RCarapinha/PreampPAL/Simulation/2.JPG

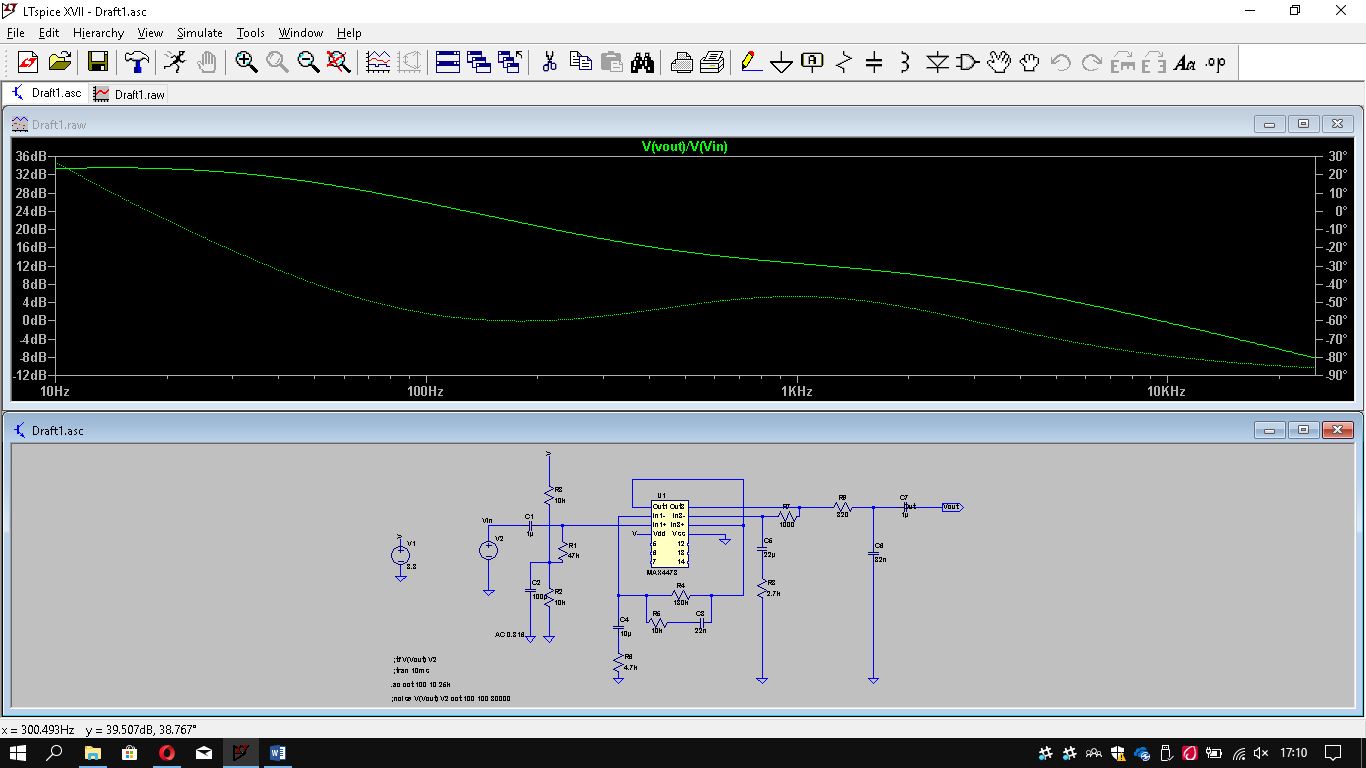
Simulation/2.JPG
