RCarapinha/PreampPAL/Simulation/3.JPG

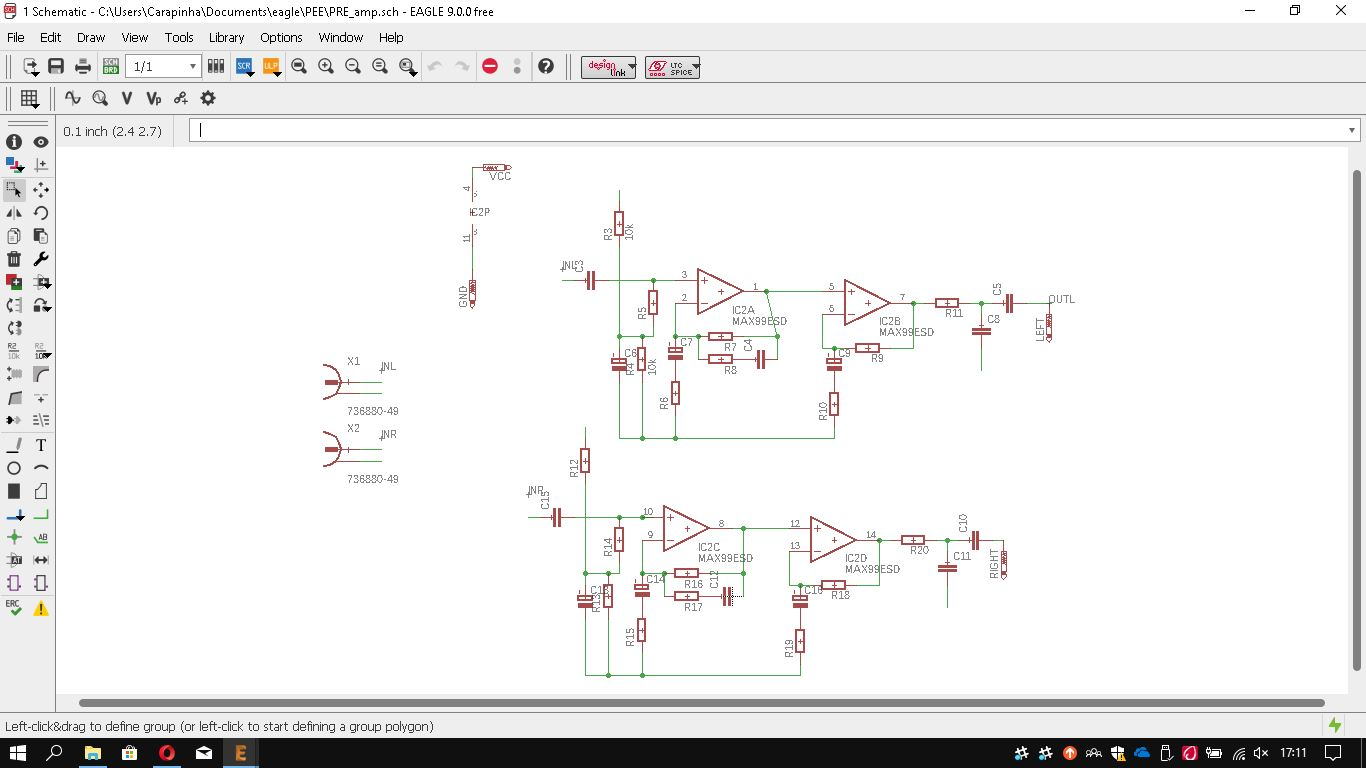
Simulation/3.JPG
