RCarapinha/PreampPAL/Simulation/4.JPG

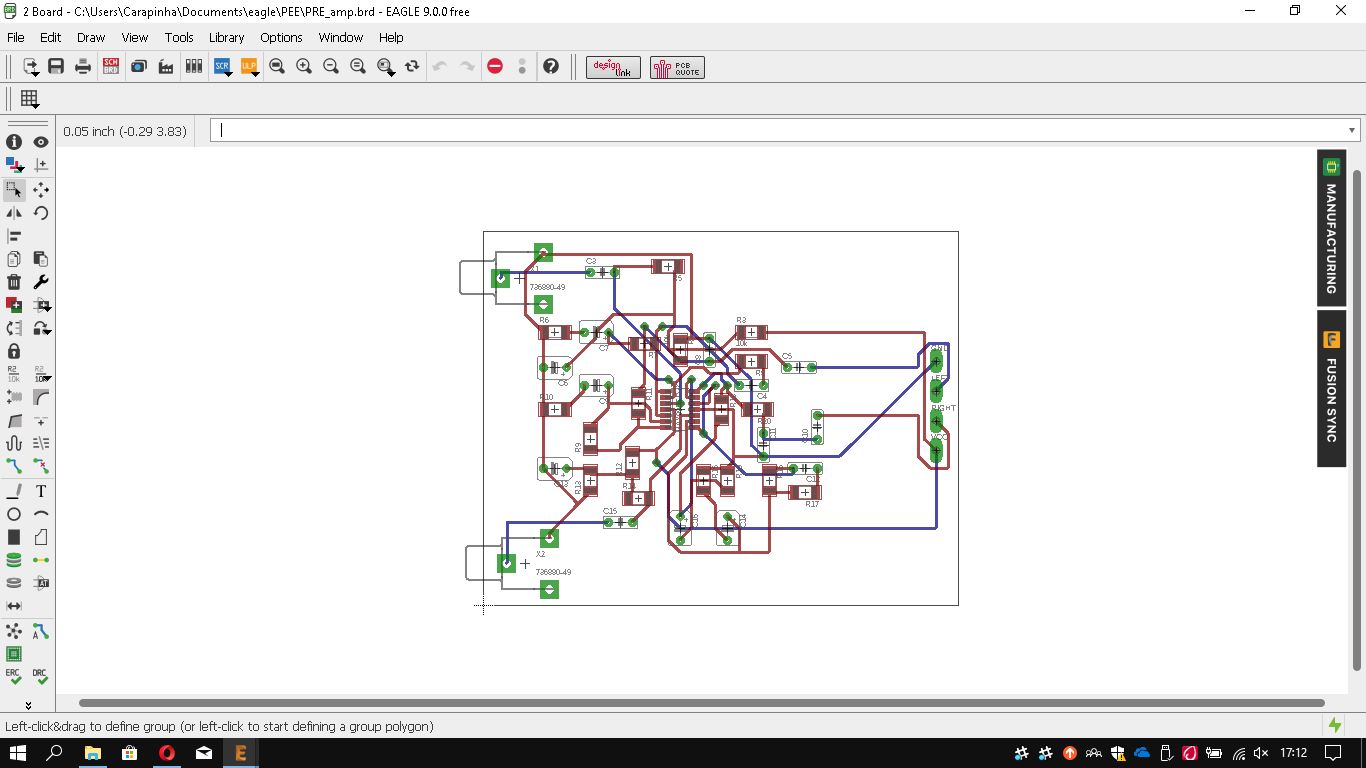
Simulation/4.JPG
