RCarapinha/PreampPAL/Simulation/Draft1.asc

C1: cap; 1µ
C2: cap; 100µ
C3: cap; 22n
C4: cap; 10µ
C5: cap; 22µ
C6: cap; 82n
C7: cap; 1µ
R1: res; 47k
R2: res; 10k
R3: res; 10k
R4: res; 180k
R5: res; 10k
R6: res; 4.7k
R7: res; 1000
R8: res; 2.7k
R9: res; 820
U1: MAX4478
V1: voltage; 3.3
V2: voltage; ""; AC 0.316
Named nets: 0, V, Out, Vout, Vin
.ac oct 100 10 25k
;noise V(Vout) V2 oct 100 100 30000
;tran 10ms
;tf V(Vout) V2
